z0r0z/cell/firmware/psbt.py

"""PSBT — parse, verify, summarise for the display, and sign.

This is where the host's claims meet the device's arithmetic. A PSBT is a
document written by software the device does not trust, and every number in it
is an assertion until the device rederives it. What this module refuses to
take on trust:

  THE INPUT AMOUNTS.  A segwit v0 signature commits to the amount of its own
      input but not the others, so a host can understate one input and the
      difference silently becomes fee. Every non-taproot input must therefore
      carry its full parent transaction, and its txid is recomputed and
      compared to the outpoint. Taproot commits to every amount at once, so
      there a witness_utxo alone is sufficient — and only there.

  WHICH OUTPUT IS CHANGE.  The host labels an output as change by attaching a
      derivation path. The device rederives the key at that path from its own
      seed, rebuilds the scriptPubKey, and compares it byte for byte to the
      output. An output that fails is shown to the owner as an unverified
      destination, in full, never folded into "change".

  THE SCRIPT TYPE.  Read from the scriptPubKey itself, never from a field the
      host supplies, because the script type selects the sighash algorithm.

  THE SIGHASH FLAG.  SIGHASH_ALL only, and an explicit PSBT_IN_SIGHASH_TYPE
      requesting anything else is a refusal rather than a downgrade.

SCOPE, deliberately: exactly one non-change output. The operation set in
ops.py is closed and BitcoinSpend renders one destination, so a batched
payment is refused rather than summarised into a total the owner cannot check
line by line. See BUILD.md section 5.
"""

from __future__ import annotations

import hashlib
from dataclasses import dataclass, field

import addresses
import ops
import secp256k1 as ec
import tx as txmod
from bip32 import ExtendedKey
from tx import Reader, Transaction, ser_compact

PSBT_MAGIC = b"psbt\xff"

# Global
GLOBAL_UNSIGNED_TX = 0x00
GLOBAL_XPUB = 0x01
GLOBAL_TX_VERSION = 0x02
GLOBAL_FALLBACK_LOCKTIME = 0x03
GLOBAL_INPUT_COUNT = 0x04
GLOBAL_OUTPUT_COUNT = 0x05
GLOBAL_TX_MODIFIABLE = 0x06
GLOBAL_VERSION = 0xFB
PROPRIETARY = 0xFC

# Per-input
IN_NON_WITNESS_UTXO = 0x00
IN_WITNESS_UTXO = 0x01
IN_PARTIAL_SIG = 0x02
IN_SIGHASH_TYPE = 0x03
IN_REDEEM_SCRIPT = 0x04
IN_WITNESS_SCRIPT = 0x05
IN_BIP32_DERIVATION = 0x06
IN_FINAL_SCRIPTSIG = 0x07
IN_FINAL_SCRIPTWITNESS = 0x08
IN_PREVIOUS_TXID = 0x0E
IN_OUTPUT_INDEX = 0x0F
IN_SEQUENCE = 0x10
IN_REQUIRED_TIME_LOCKTIME = 0x11
IN_REQUIRED_HEIGHT_LOCKTIME = 0x12
IN_TAP_KEY_SIG = 0x13
IN_TAP_BIP32_DERIVATION = 0x16
IN_TAP_INTERNAL_KEY = 0x17

# Per-output
OUT_REDEEM_SCRIPT = 0x00
OUT_WITNESS_SCRIPT = 0x01
OUT_BIP32_DERIVATION = 0x02
OUT_AMOUNT = 0x03
OUT_SCRIPT = 0x04
OUT_TAP_INTERNAL_KEY = 0x05
OUT_TAP_BIP32_DERIVATION = 0x07

# A fee this large is more likely a lie about an input amount than a generous
# tip. It is NOT a refusal, and the comment here used to say it was: the fee
# gets its own line on the confirmation screen in full, and
# ops.BitcoinSpend.amount_for_policy prices it into the tier floor, so a spend
# carrying its value in the fee escalates to blood on the amount alone. This
# constant only flags it in Summary.warnings, which is machine-readable
# context for a caller and never reaches the panel.
ABSURD_FEE_SATS = 10_000_000


class BadPSBT(ValueError):
    """A PSBT this device will not sign, and why."""


# --------------------------------------------------------------------------
# Key-value maps
# --------------------------------------------------------------------------

KVMap = dict[bytes, bytes]


def _parse_map(r: Reader) -> KVMap:
    out: KVMap = {}
    while True:
        klen = r.compact()
        if klen == 0:
            return out
        key = r.read(klen)
        val = r.bytes_with_len()
        if key in out:
            # Duplicate keys are explicitly invalid in BIP-174. Accepting them
            # means the device and the host may disagree about which value
            # applies, which is a disagreement about what is being signed.
            raise BadPSBT(f"duplicate key {key.hex()} in a PSBT map")
        out[key] = val


def _ser_map(m: KVMap) -> bytes:
    out = b""
    for k in sorted(m):
        out += ser_compact(len(k)) + k + ser_compact(len(m[k])) + m[k]
    return out + b"\x00"


def _get(m: KVMap, keytype: int) -> bytes | None:
    return m.get(bytes([keytype]))


def _get_all(m: KVMap, keytype: int) -> dict[bytes, bytes]:
    """Every entry of this type, mapped by the key's data suffix."""
    return {k[1:]: v for k, v in m.items() if k and k[0] == keytype and len(k) > 1}


def proprietary_key(identifier: bytes, subtype: int = 0,
                    keydata: bytes = b"") -> bytes:
    """A BIP-174 proprietary key.

        0xFC <compact len(identifier)> <identifier> <compact subtype> <keydata>

    The length prefix is the whole point and is easy to leave out, because
    `0xFC` followed by a vendor string looks complete. It is not: a parser
    reads the byte after 0xFC as the identifier's length, so `0xFC "CELL" 01`
    tells it the identifier is 0x43 = 67 bytes long, and it runs off the end
    of the map. Bitcoin Core rejects such a PSBT outright with a decode error
    — it does not skip the field it cannot read — so an attestation written
    this way makes the whole transaction unreadable to the coordinator that
    has to finalise it.

    This was found by handing a signed PSBT to a real node. No amount of
    round-tripping through our own parser would have shown it, because our own
    parser treats the key as an opaque blob and never looks inside.
    """
    return (bytes([PROPRIETARY]) + ser_compact(len(identifier)) + identifier
            + ser_compact(subtype) + keydata)


def _parse_derivation(val: bytes) -> tuple[bytes, list[int]]:
    if len(val) < 4 or (len(val) - 4) % 4:
        raise BadPSBT("malformed BIP32 derivation field")
    fp = val[:4]
    path = [int.from_bytes(val[i:i + 4], "little") for i in range(4, len(val), 4)]
    return fp, path


def _ser_derivation(fp: bytes, path: list[int]) -> bytes:
    return fp + b"".join(i.to_bytes(4, "little") for i in path)


# --------------------------------------------------------------------------
# BIP-370 (version 2) reconstruction
#
# Version 2 removes the global unsigned transaction and scatters its fields
# across the input and output maps instead. Nothing about what the device
# checks changes: we rebuild the transaction those fields describe and then
# run exactly the same verification over it. Doing it this way rather than
# threading a second representation through psbt.py means there is one set of
# rules about amounts, change and sighashes, not two that could drift.
# --------------------------------------------------------------------------


def _count(g: KVMap, keytype: int, what: str) -> int:
    raw = _get(g, keytype)
    if raw is None:
        raise BadPSBT(f"a version 2 PSBT must declare its {what} count")
    r = Reader(raw)
    n = r.compact()
    if not r.done:
        raise BadPSBT(f"trailing bytes in the {what} count")
    if not 0 < n <= 4096:
        raise BadPSBT(f"{what} count of {n} is out of range")
    return n


def _rebuild_v2(g: KVMap, in_maps: list[KVMap], out_maps: list[KVMap]) -> Transaction:
    ver_raw = _get(g, GLOBAL_TX_VERSION)
    if ver_raw is None or len(ver_raw) != 4:
        raise BadPSBT("a version 2 PSBT must declare a 4-byte transaction version")
    tx = Transaction(version=int.from_bytes(ver_raw, "little"))

    for i, m in enumerate(in_maps):
        txid = _get(m, IN_PREVIOUS_TXID)
        index = _get(m, IN_OUTPUT_INDEX)
        if txid is None or len(txid) != 32:
            raise BadPSBT(f"input {i} has no 32-byte previous txid")
        if index is None or len(index) != 4:
            raise BadPSBT(f"input {i} has no 4-byte output index")
        seq = _get(m, IN_SEQUENCE)
        if seq is not None and len(seq) != 4:
            raise BadPSBT(f"input {i} has a malformed sequence")
        tx.vin.append(txmod.TxIn(
            txid=txid, vout=int.from_bytes(index, "little"),
            sequence=int.from_bytes(seq, "little") if seq else 0xFFFFFFFF))

    for i, m in enumerate(out_maps):
        amount = _get(m, OUT_AMOUNT)
        script = _get(m, OUT_SCRIPT)
        if amount is None or len(amount) != 8:
            raise BadPSBT(f"output {i} has no 8-byte amount")
        if script is None:
            raise BadPSBT(f"output {i} has no script")
        value = int.from_bytes(amount, "little", signed=True)
        if value < 0:
            raise BadPSBT(f"output {i} has a negative amount")
        tx.vout.append(txmod.TxOut(value=value, script_pubkey=script))

    tx.locktime = _v2_locktime(g, in_maps)
    return tx


def _v2_locktime(g: KVMap, in_maps: list[KVMap]) -> int:
    """The locktime BIP-370 says this transaction ends up with.

    An input may REQUIRE a height or a time locktime. If any does, the
    transaction takes the largest requirement of that kind and the fallback is
    ignored. Requiring both kinds at once is not satisfiable, and a device that
    picked one would be signing a transaction different from the one the
    coordinator meant — so that is a refusal.
    """
    heights, times = [], []
    for i, m in enumerate(in_maps):
        h, t = _get(m, IN_REQUIRED_HEIGHT_LOCKTIME), _get(m, IN_REQUIRED_TIME_LOCKTIME)
        if h is not None:
            if len(h) != 4:
                raise BadPSBT(f"input {i} has a malformed height locktime")
            heights.append(int.from_bytes(h, "little"))
        if t is not None:
            if len(t) != 4:
                raise BadPSBT(f"input {i} has a malformed time locktime")
            times.append(int.from_bytes(t, "little"))
    if heights and times:
        raise BadPSBT(
            "this PSBT requires both a height locktime and a time locktime, "
            "which no single transaction can satisfy")
    if heights:
        return max(heights)
    if times:
        return max(times)
    fallback = _get(g, GLOBAL_FALLBACK_LOCKTIME)
    if fallback is None:
        return 0
    if len(fallback) != 4:
        raise BadPSBT("malformed fallback locktime")
    return int.from_bytes(fallback, "little")


# --------------------------------------------------------------------------
# Multisig descriptors — the registered co-signers
# --------------------------------------------------------------------------


@dataclass
class MultisigDescriptor:
    """An m-of-n the device has been told about, and can therefore rebuild.

    THIS IS WHY REGISTRATION EXISTS. Without it, "is this output ours?" can
    only be answered as "does it contain a key of mine?" — and an attacker who
    controls the coordinator can build a script holding exactly one key of
    yours and n-1 of theirs. It hashes correctly, the wallet calls it change,
    and the balance moves to a script you cannot spend without them.

    With the co-signers registered the question becomes "does this output
    equal the script my registered quorum produces at the path it claims?",
    which is arithmetic and cannot be talked around.

    `keys` are (master fingerprint, account path, account xpub), one per
    co-signer, in the order the descriptor declares. `sorted_keys` is BIP-67
    lexicographic ordering, which most coordinators default to; getting it
    wrong produces a different address rather than an error, so it is recorded
    rather than guessed.
    """

    threshold: int
    keys: list[tuple[bytes, list[int], ExtendedKey]]
    sorted_keys: bool = True
    wrapped: bool = False               # p2sh-p2wsh rather than bare p2wsh
    label: str = ""

    @property
    def n(self) -> int:
        return len(self.keys)

    def witness_script_for(self, derivations: dict[bytes, bytes]) -> bytes | None:
        """Rebuild the witness script these derivations claim, or None.

        Every registered co-signer must appear exactly once, at the same
        change/index suffix as the others. A PSBT that quotes a different
        suffix for one co-signer is not describing a standard multisig
        address, and guessing which one it meant is how a wallet ends up
        confident about the wrong script.
        """
        found: list[bytes] = []
        suffix: list[int] | None = None
        for fp, prefix, xpub in self.keys:
            match = None
            for keybytes, val in derivations.items():
                try:
                    origin_fp, path = _parse_derivation(val)
                except BadPSBT:
                    return None
                if origin_fp != fp or path[:len(prefix)] != prefix:
                    continue
                if match is not None:
                    return None                 # ambiguous; refuse to guess
                match = (keybytes, path[len(prefix):])
            if match is None:
                return None
            keybytes, tail = match
            if suffix is None:
                suffix = tail
            elif tail != suffix:
                return None
            try:
                if xpub.derive(tail).pubkey != keybytes:
                    return None
            except ValueError:
                return None
            found.append(keybytes)

        if len(found) != self.n or not 1 <= self.threshold <= self.n:
            return None
        ordered = sorted(found) if self.sorted_keys else found
        try:
            return addresses.multisig_script(self.threshold, ordered)
        except addresses.BadAddress:
            return None

    def script_pubkey_for(self, derivations: dict[bytes, bytes]) -> bytes | None:
        ws = self.witness_script_for(derivations)
        if ws is None:
            return None
        p2wsh = addresses.p2wsh_script(ws)
        return addresses.p2sh_script(p2wsh) if self.wrapped else p2wsh

    def script_pubkey_at(self, change: int, index: int) -> bytes:
        """The scriptPubKey this quorum produces at one derivation suffix.

        The methods above answer "is this output ours?" from what a PSBT
        claims. This one asks the question forwards, from the descriptor
        alone, so the device can SHOW an address rather than only recognise
        one. Same ordering rule, same wrapping, same arithmetic -- deliberately
        the same code path as far as `multisig_script`, because an address the
        device displays and an output it recognises that disagreed would be a
        quorum whose owner funds one wallet and watches another.
        """
        if not 1 <= self.threshold <= self.n:
            raise addresses.BadAddress(
                f"{self.threshold} of {self.n} is not a usable quorum")
        pubkeys = [xpub.derive([change, index]).pubkey
                   for _fp, _prefix, xpub in self.keys]
        ordered = sorted(pubkeys) if self.sorted_keys else pubkeys
        p2wsh = addresses.p2wsh_script(
            addresses.multisig_script(self.threshold, ordered))
        return addresses.p2sh_script(p2wsh) if self.wrapped else p2wsh

    def address_at(self, change: int, index: int,
                   network: str = "mainnet") -> str:
        return addresses.script_to_address(
            self.script_pubkey_at(change, index), network)


# --------------------------------------------------------------------------
# Per-input analysis
# --------------------------------------------------------------------------


@dataclass
class InputInfo:
    """Everything the device worked out for itself about one input."""

    index: int
    amount: int
    script_pubkey: bytes
    kind: str                       # p2pkh / p2sh / p2wpkh / p2wsh / p2sh-p2wpkh / p2tr
    script_code: bytes = b""        # what a v0 or legacy sighash covers
    witness_script: bytes = b""
    amount_verified: bool = False   # by a txid-verified parent transaction
    ours: list[tuple[bytes, list[int]]] = field(default_factory=list)
    quorum_needed: int = 0
    quorum_size: int = 0
    sigs_present: int = 0
    descriptor: "MultisigDescriptor | None" = None


def _classify(spk: bytes) -> str:
    if len(spk) == 25 and spk[:3] == b"\x76\xa9\x14" and spk[23:] == b"\x88\xac":
        return "p2pkh"
    if len(spk) == 23 and spk[:2] == b"\xa9\x14" and spk[22:] == b"\x87":
        return "p2sh"
    if len(spk) == 22 and spk[:2] == b"\x00\x14":
        return "p2wpkh"
    if len(spk) == 34 and spk[:2] == b"\x00\x20":
        return "p2wsh"
    if len(spk) == 34 and spk[:2] == b"\x51\x20":
        return "p2tr"
    raise BadPSBT(f"input has an unsupported script type ({spk[:4].hex()}…). "
                  f"This device signs p2pkh, p2sh, p2wpkh, p2wsh and p2tr.")


def parse_multisig(script: bytes) -> tuple[int, list[bytes]]:
    """(m, keys) from a bare CHECKMULTISIG script, or (0, []).

    Strict on purpose. The loose version of this — read the first and last
    opcodes, trust the middle — will happily report "2 of 3" for a script
    whose middle is something else entirely, and that number goes on the
    screen the owner approves. So every push is walked, every key must be a
    33-byte compressed point on the curve, and the declared n must equal the
    number of keys actually present.
    """
    if len(script) < 3 + 34 or script[-1] != 0xAE:
        return 0, []
    m, n = script[0] - 0x50, script[-2] - 0x50
    if not (1 <= m <= n <= 16):
        return 0, []
    keys, i = [], 1
    while i < len(script) - 2:
        if script[i] != 33 or i + 34 > len(script) - 2:
            return 0, []
        key = script[i + 1:i + 34]
        try:
            ec.parse_pubkey(key)
        except ec.BadKey:
            return 0, []
        keys.append(key)
        i += 34
    if i != len(script) - 2 or len(keys) != n:
        return 0, []
    return m, keys


def _parse_multisig(script: bytes) -> tuple[int, int]:
    """(m, n), or (0, 0). Convenience over parse_multisig."""
    m, keys = parse_multisig(script)
    return (m, len(keys)) if m else (0, 0)


# --------------------------------------------------------------------------


@dataclass
class Summary:
    """What the device concluded, and what it will show the owner."""

    spend: ops.BitcoinSpend
    inputs: list[InputInfo]
    total_in: int
    fee: int
    signable: int                   # inputs this device holds a key for
    warnings: list[str] = field(default_factory=list)
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
